bigtreetech/BIQU-B1/Firmware/2021-04-28/Screen-210609/Language Packs/语言包详情.bmp

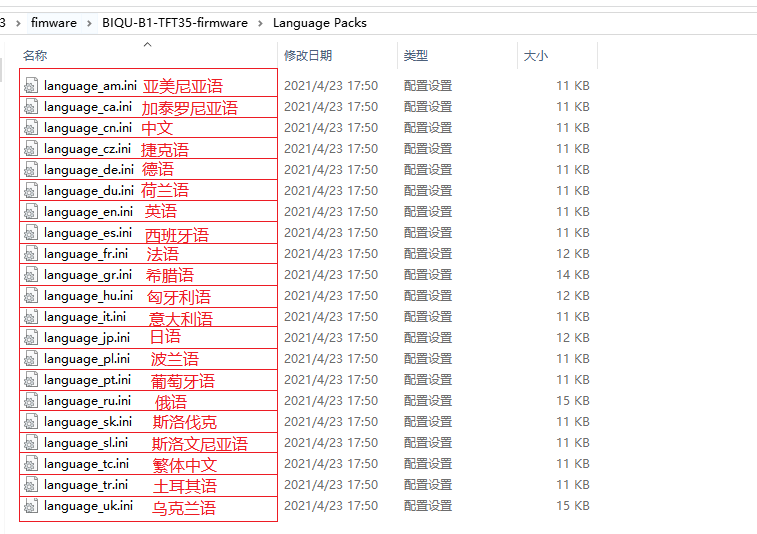
Firmware/2021-04-28/Screen-210609/Language Packs/语言包详情.bmp
